flavioafferreira/datacollector/FusionCircuit/DataCollectorV1 v1_bot.png

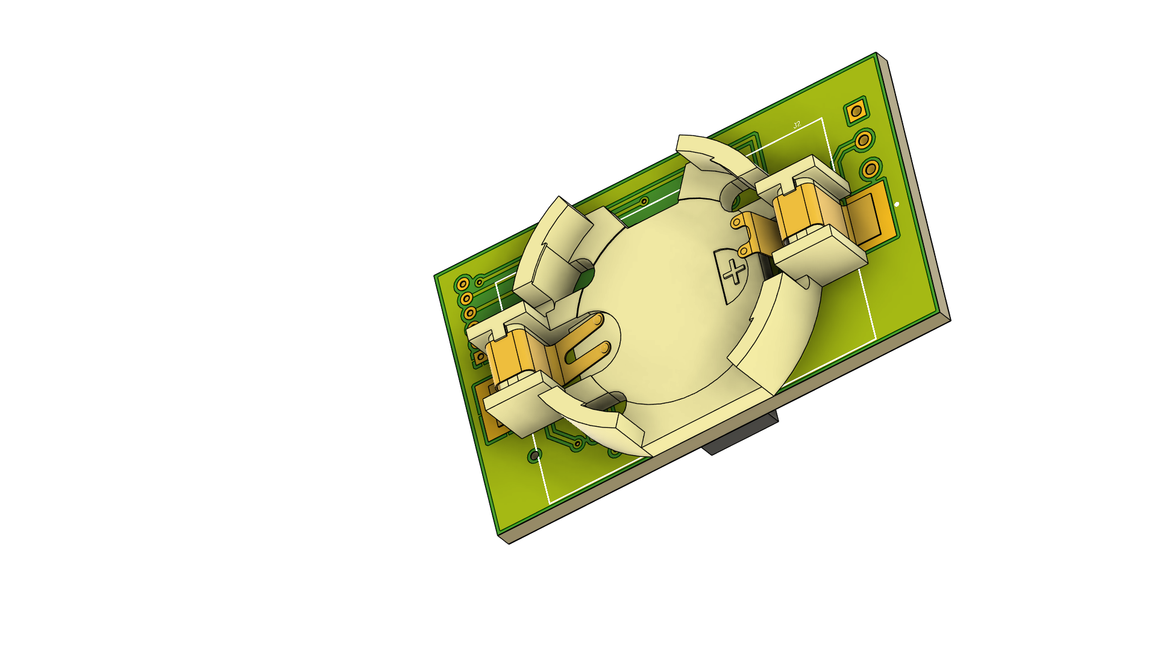
FusionCircuit/DataCollectorV1 v1_bot.png
