flavioafferreira/datacollector/FusionCircuit/DataCollectorV1 v1_top.png

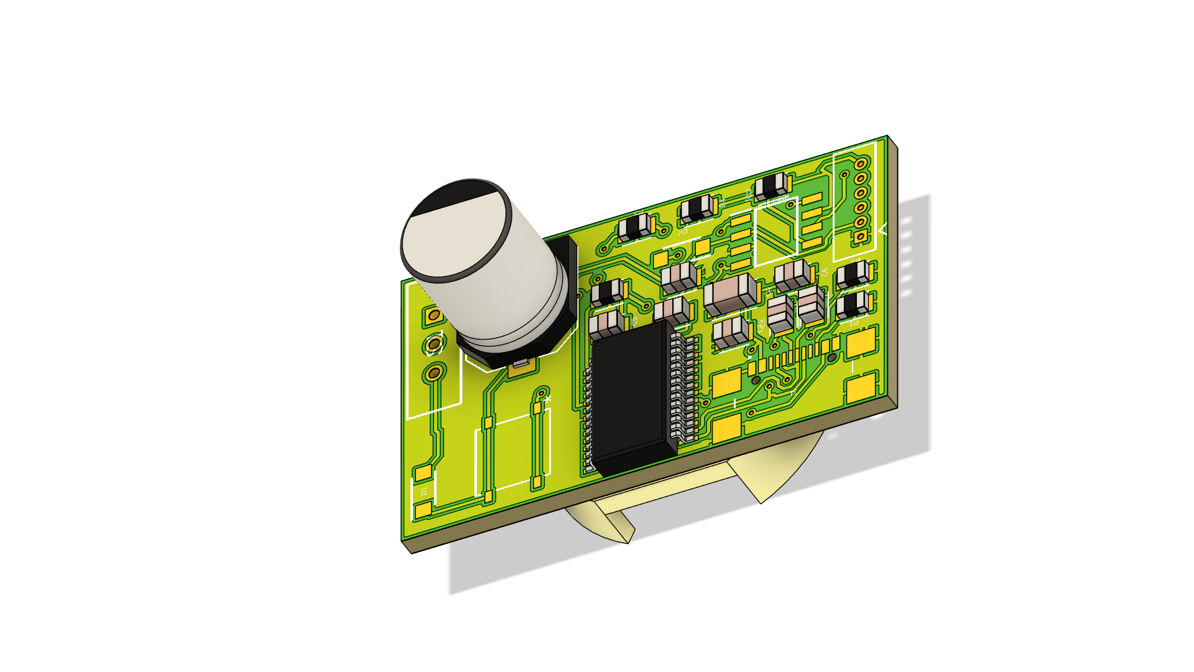
FusionCircuit/DataCollectorV1 v1_top.png
