flavioafferreira/datacollector/FusionCircuit/WhatsApp Image 2025-08-05 at 14.06.19.jpeg

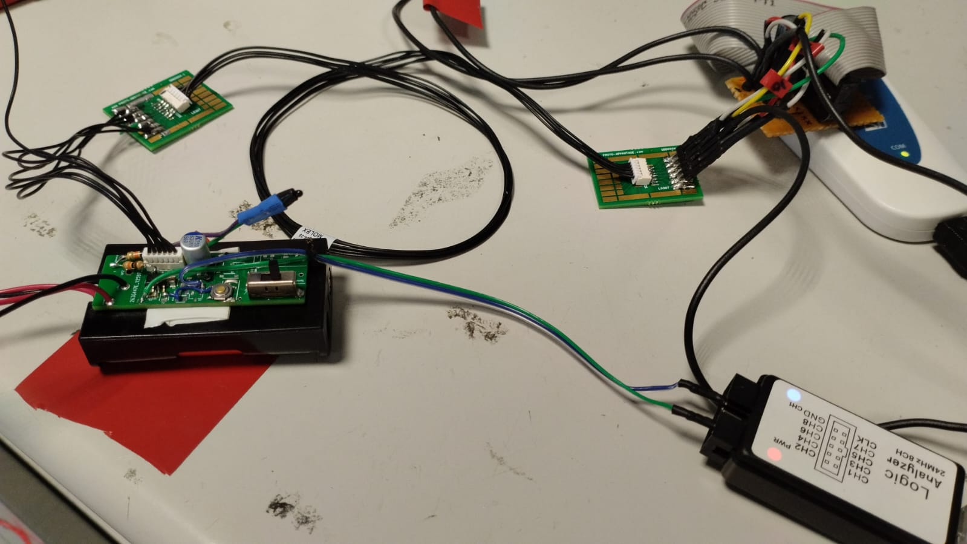
FusionCircuit/WhatsApp Image 2025-08-05 at 14.06.19.jpeg
