flavioafferreira/datacollector/Images/adjust_top.jpeg

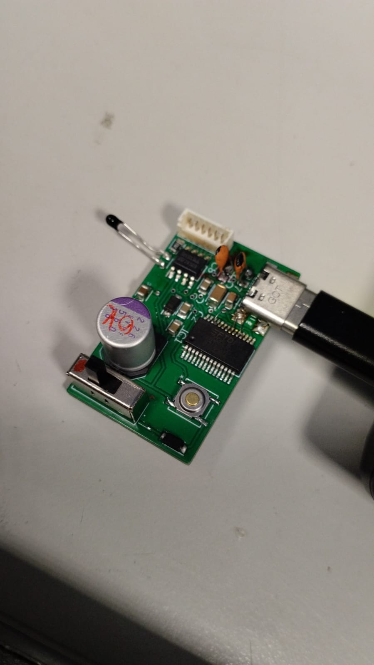
Images/adjust_top.jpeg
