flavioafferreira/datacollector/Core/Src/usart.c

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
/* Includes ------------------------------------------------------------------*/
#include "usart.h"

/* USER CODE BEGIN 0 */


#include <string.h>


char rx_buffer[RX_BUFFER_SIZE];
char rx_buffer_intern[RX_BUFFER_SIZE];
int rx_index = 0;


/* USER CODE END 0 */

/* USART1 init function */

void MX_USART1_UART_Init(void)
{

  LL_USART_InitTypeDef USART_InitStruct = {0};

  LL_GPIO_InitTypeDef GPIO_InitStruct = {0};

  LL_RCC_SetUSARTClockSource(LL_RCC_USART1_CLKSOURCE_PCLK1);

  /* Peripheral clock enable */
  LL_APB2_GRP1_EnableClock(LL_APB2_GRP1_PERIPH_USART1);

  LL_IOP_GRP1_EnableClock(LL_IOP_GRP1_PERIPH_GPIOC);
  LL_IOP_GRP1_EnableClock(LL_IOP_GRP1_PERIPH_GPIOA);
  /**USART1 GPIO Configuration
  PC14-OSCX_IN (PC14)   ------> USART1_TX
  PA8   ------> USART1_RX
  */
  GPIO_InitStruct.Pin = TX_Pin;
  GPIO_InitStruct.Mode = LL_GPIO_MODE_ALTERNATE;
  GPIO_InitStruct.Speed = LL_GPIO_SPEED_FREQ_LOW;
  GPIO_InitStruct.OutputType = LL_GPIO_OUTPUT_PUSHPULL;
  GPIO_InitStruct.Pull = LL_GPIO_PULL_NO;
  GPIO_InitStruct.Alternate = LL_GPIO_AF_0;
  LL_GPIO_Init(TX_GPIO_Port, &GPIO_InitStruct);

  GPIO_InitStruct.Pin = RX_Pin;
  GPIO_InitStruct.Mode = LL_GPIO_MODE_ALTERNATE;
  GPIO_InitStruct.Speed = LL_GPIO_SPEED_FREQ_LOW;
  GPIO_InitStruct.OutputType = LL_GPIO_OUTPUT_OPENDRAIN;
  GPIO_InitStruct.Pull = LL_GPIO_PULL_NO;
  GPIO_InitStruct.Alternate = LL_GPIO_AF_14;
  LL_GPIO_Init(RX_GPIO_Port, &GPIO_InitStruct);

  LL_SYSCFG_ConfigPinMux(LL_PINMUX_SO8_PIN1_PC14);

  LL_SYSCFG_ConfigPinMux(LL_PINMUX_SO8_PIN5_PA8);

  /* USART1 interrupt Init */
  NVIC_SetPriority(USART1_IRQn, 0);
  NVIC_EnableIRQ(USART1_IRQn);

  USART_InitStruct.PrescalerValue = LL_USART_PRESCALER_DIV1;
  USART_InitStruct.BaudRate = 1200;
  USART_InitStruct.DataWidth = LL_USART_DATAWIDTH_8B;
  USART_InitStruct.StopBits = LL_USART_STOPBITS_1;
  USART_InitStruct.Parity = LL_USART_PARITY_NONE;
  USART_InitStruct.TransferDirection = LL_USART_DIRECTION_TX_RX;
  USART_InitStruct.HardwareFlowControl = LL_USART_HWCONTROL_NONE;
  USART_InitStruct.OverSampling = LL_USART_OVERSAMPLING_16;
  LL_USART_Init(USART1, &USART_InitStruct);
  LL_USART_SetTXFIFOThreshold(USART1, LL_USART_FIFOTHRESHOLD_1_8);
  LL_USART_SetRXFIFOThreshold(USART1, LL_USART_FIFOTHRESHOLD_1_8);
  LL_USART_DisableFIFO(USART1);
  LL_USART_ConfigAsyncMode(USART1);

  /* USER CODE BEGIN WKUPType USART1 */

   //LL_USART_EnableIT_RXNE(USART1);

  /* USER CODE END WKUPType USART1 */

  LL_USART_Enable(USART1);

  /* Polling USART1 initialisation */
  while((!(LL_USART_IsActiveFlag_TEACK(USART1))) || (!(LL_USART_IsActiveFlag_REACK(USART1))))
  {
  }
}

/* USER CODE BEGIN 1 */


void usart1_interrupt_handler(void){
    uint8_t data;

    // Verificar se a interrupção é de recepção de dados (RXNE)
    if (LL_USART_IsActiveFlag_RXNE(USART1))
    {
    	//marker(2);
        // Ler o dado recebido
        data = LL_USART_ReceiveData8(USART1);

        // Armazenar o dado no buffer até o caractere '\n' ou até o buffer ficar cheio
        if (data == '\n' || data == '\r' || rx_index >= RX_BUFFER_SIZE - 1)
        {

            rx_buffer_intern[rx_index] = '\0';  // Termina a string

            memcpy(rx_buffer, rx_buffer_intern, rx_index + 1);
            rx_index = 0;  // Resetar o índice para o próximo recebimento
            //USAR O SEMAFORO xSemaphoreGive(xSemaphoreSerialRX);
            //transferir o conteudo do buffer para outra variavel disponivel

        }
        else
        {
            rx_buffer_intern[rx_index++] = data;  // Armazenar o dado no buffer
        }
    }
}





void MX_USART1_UART_Init_New(void)
{

  LL_USART_InitTypeDef USART_InitStruct = {0};
  LL_GPIO_InitTypeDef GPIO_InitStruct = {0};
  LL_RCC_SetUSARTClockSource(LL_RCC_USART1_CLKSOURCE_PCLK1);
  LL_APB2_GRP1_EnableClock(LL_APB2_GRP1_PERIPH_USART1);

  LL_IOP_GRP1_EnableClock(LL_IOP_GRP1_PERIPH_GPIOC);
  LL_IOP_GRP1_EnableClock(LL_IOP_GRP1_PERIPH_GPIOA);
  GPIO_InitStruct.Pin = TX_Pin;
  GPIO_InitStruct.Mode = LL_GPIO_MODE_ALTERNATE;
  GPIO_InitStruct.Speed = LL_GPIO_SPEED_FREQ_LOW;
  GPIO_InitStruct.OutputType = LL_GPIO_OUTPUT_PUSHPULL;
  GPIO_InitStruct.Pull = LL_GPIO_PULL_NO;
  GPIO_InitStruct.Alternate = LL_GPIO_AF_0;
  LL_GPIO_Init(TX_GPIO_Port, &GPIO_InitStruct);



  GPIO_InitStruct.Pin = RX_Pin;
   GPIO_InitStruct.Mode = LL_GPIO_MODE_ALTERNATE;
   GPIO_InitStruct.Speed = LL_GPIO_SPEED_FREQ_LOW;
   GPIO_InitStruct.OutputType = LL_GPIO_OUTPUT_OPENDRAIN;
   GPIO_InitStruct.Pull = LL_GPIO_PULL_NO;
   GPIO_InitStruct.Alternate = LL_GPIO_AF_14;
   LL_GPIO_Init(RX_GPIO_Port, &GPIO_InitStruct);

   LL_SYSCFG_ConfigPinMux(LL_PINMUX_SO8_PIN1_PC14);

   LL_SYSCFG_ConfigPinMux(LL_PINMUX_SO8_PIN5_PA8);


  NVIC_SetPriority(USART1_IRQn, 0);
  NVIC_EnableIRQ(USART1_IRQn);

  USART_InitStruct.PrescalerValue = LL_USART_PRESCALER_DIV1;
  USART_InitStruct.BaudRate = 1200;
  USART_InitStruct.DataWidth = LL_USART_DATAWIDTH_8B;
  USART_InitStruct.StopBits = LL_USART_STOPBITS_1;
  USART_InitStruct.Parity = LL_USART_PARITY_NONE;
  USART_InitStruct.TransferDirection = LL_USART_DIRECTION_TX_RX;
  USART_InitStruct.HardwareFlowControl = LL_USART_HWCONTROL_NONE;
  USART_InitStruct.OverSampling = LL_USART_OVERSAMPLING_16;
  LL_USART_Init(USART1, &USART_InitStruct);
  LL_USART_SetTXFIFOThreshold(USART1, LL_USART_FIFOTHRESHOLD_1_8);
  LL_USART_SetRXFIFOThreshold(USART1, LL_USART_FIFOTHRESHOLD_1_8);
  LL_USART_DisableFIFO(USART1);
  LL_USART_ConfigAsyncMode(USART1);


  LL_USART_Enable(USART1);
  LL_USART_EnableIT_RXNE(USART1);

  /* Polling USART1 initialisation */
  while((!(LL_USART_IsActiveFlag_TEACK(USART1))) || (!(LL_USART_IsActiveFlag_REACK(USART1))))
  {
  }

}


/* USER CODE END 1 */
