flavioafferreira/datacollector/Core/Src/gpio.c

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

/* Includes ------------------------------------------------------------------*/
#include "gpio.h"

/*----------------------------------------------------------------------------*/
/* Configure GPIO                                                             */
/*----------------------------------------------------------------------------*/
/** Configure pins
*/
void MX_GPIO_Init(void)
{

  LL_GPIO_InitTypeDef GPIO_InitStruct = {0};

  /* GPIO Ports Clock Enable */
  LL_IOP_GRP1_EnableClock(LL_IOP_GRP1_PERIPH_GPIOC);
  LL_IOP_GRP1_EnableClock(LL_IOP_GRP1_PERIPH_GPIOA);

  /**/
  LL_GPIO_ResetOutputPin(alim_ntc_GPIO_Port, alim_ntc_Pin);

  /**/
  GPIO_InitStruct.Pin = alim_ntc_Pin;
  GPIO_InitStruct.Mode = LL_GPIO_MODE_OUTPUT;
  GPIO_InitStruct.Speed = LL_GPIO_SPEED_FREQ_LOW;
  GPIO_InitStruct.OutputType = LL_GPIO_OUTPUT_PUSHPULL;
  GPIO_InitStruct.Pull = LL_GPIO_PULL_NO;
  LL_GPIO_Init(alim_ntc_GPIO_Port, &GPIO_InitStruct);

}

/* USER CODE BEGIN 2 */
void Pin_Config_NTC_Alim(void){
	LL_GPIO_InitTypeDef GPIO_InitStruct = {0};

	/** Configure alim_ntc as output BEFORE setting its value */
	  GPIO_InitStruct.Pin = alim_ntc_Pin;
	  GPIO_InitStruct.Mode = LL_GPIO_MODE_OUTPUT;
	  GPIO_InitStruct.Speed = LL_GPIO_SPEED_FREQ_LOW;
	  GPIO_InitStruct.OutputType = LL_GPIO_OUTPUT_PUSHPULL;
	  GPIO_InitStruct.Pull = LL_GPIO_PULL_NO;
	  LL_GPIO_Init(alim_ntc_GPIO_Port, &GPIO_InitStruct);
	  /* Now it's safe to set it high */
	  LL_GPIO_SetOutputPin(alim_ntc_GPIO_Port, alim_ntc_Pin);
}

void Pin_Config_NTC_Disable(void){
	   LL_GPIO_InitTypeDef GPIO_InitStruct = {0};
	    GPIO_InitStruct.Pin = alim_ntc_Pin;
	    GPIO_InitStruct.Mode = LL_GPIO_MODE_INPUT;
	    GPIO_InitStruct.Pull = LL_GPIO_PULL_DOWN; // ou LL_GPIO_PULL_UP se preferir
	    LL_GPIO_Init(alim_ntc_GPIO_Port, &GPIO_InitStruct);
}



/* USER CODE END 2 */
